Pl0p/Gate_O_Matix/Kicad_Project/My_library/Mes_modèles_3D/bh-connector-set-1.snapshot.1/BH-16R.STEP

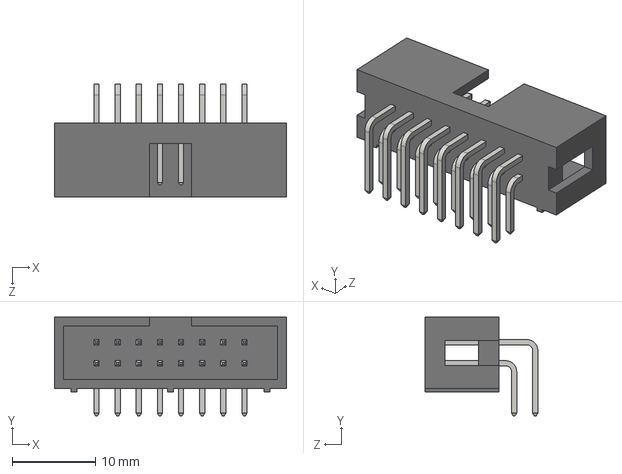
[picture p14: CAD file, 2021-02-21]
Kicad_Project/My_library/Mes_modèles_3D/bh-connector-set-1.snapshot.1/BH-16R.STEP
27.9 x 11.9 x 13.6 mm
