Pl0p/Gate_O_Matix/Kicad_Project/My_library/Mes_modèles_3D/Encoders/EC11B-SW-Vert-20F-green.step

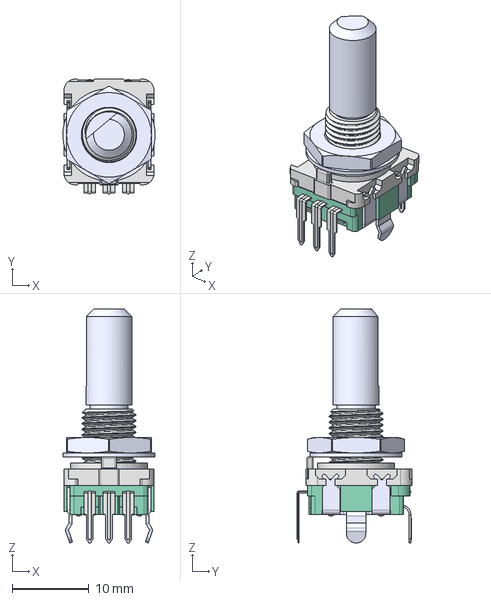
[picture p15: CAD file, 2021-02-21]
Kicad_Project/My_library/Mes_modèles_3D/Encoders/EC11B-SW-Vert-20F-green.step
12.0 x 14.9 x 30.4 mm
