Pl0p/Gate_O_Matix/Kicad_Project/My_library/Mes_modèles_3D/Encoders/EC11B-SW-Vert-15K-blue.step

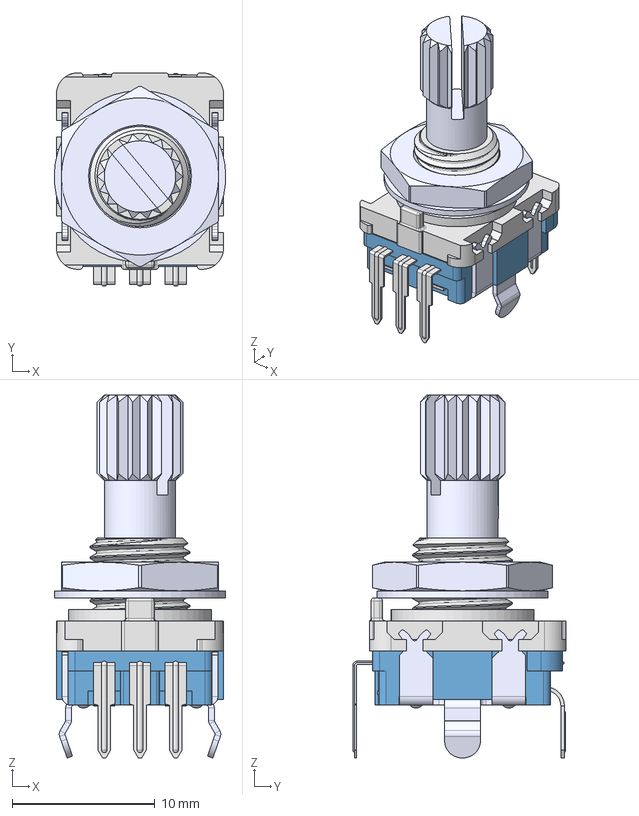
[picture p20: CAD file, 2021-02-21]
Kicad_Project/My_library/Mes_modèles_3D/Encoders/EC11B-SW-Vert-15K-blue.step
12.0 x 14.9 x 25.4 mm
