Pl0p/Gate_O_Matix/Kicad_Project/My_library/Mes_modèles_3D/IC_Sockets/DIP-32 W7.62mm IC with Socket.stp

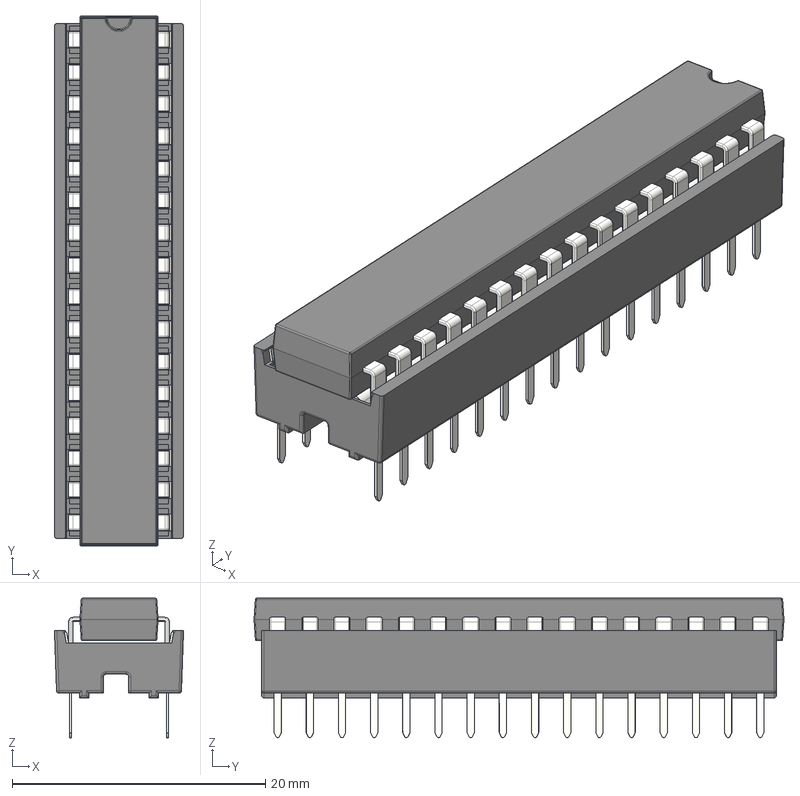
[picture p21: CAD file, 2021-02-21]
Kicad_Project/My_library/Mes_modèles_3D/IC_Sockets/DIP-32 W7.62mm IC with Socket.stp
10.2 x 41.8 x 11.0 mm
Stamped Dual Wipe Contact for DIP Sockets x 32
Body DIP-48 Socket
IC Beinchen x 32
DIP-32 W7.62
