Pl0p/Gate_O_Matix/Kicad_Project/My_library/Mes_modèles_3D/IC_Sockets/DIP-18 W7.62mm IC with Socket.stp

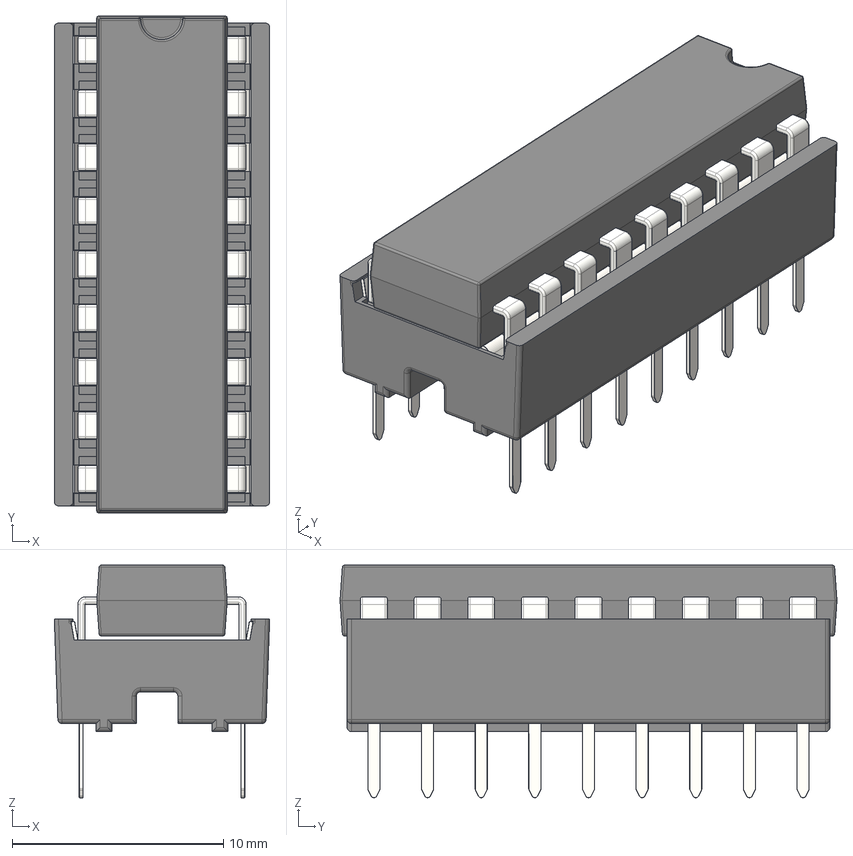
[picture p22: CAD file, 2021-02-21]
Kicad_Project/My_library/Mes_modèles_3D/IC_Sockets/DIP-18 W7.62mm IC with Socket.stp
10.2 x 23.5 x 11.0 mm
Stamped Dual Wipe Contact for DIP Sockets x 18
Body DIP-18 P7.62mm Socket
IC Beinchen x 18
DIP-18 W7.62
