Pl0p/Gate_O_Matix/Kicad_Project/My_library/Mes_modèles_3D/Encoders/EC11B-SW-Vert-20K-green.step

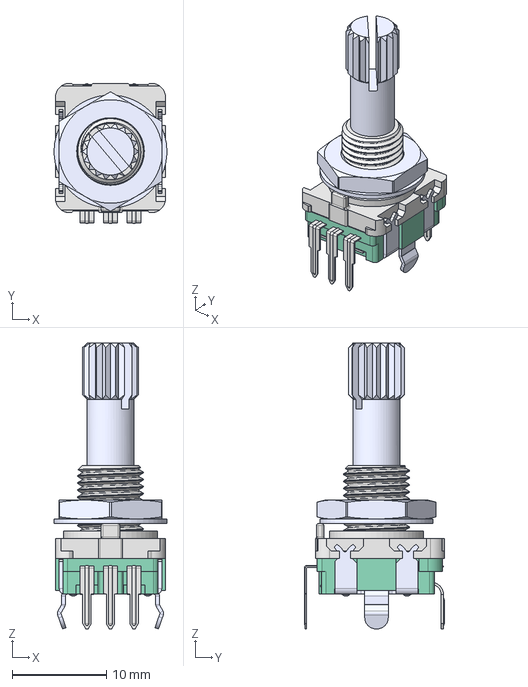
[picture p23: CAD file, 2021-02-21]
Kicad_Project/My_library/Mes_modèles_3D/Encoders/EC11B-SW-Vert-20K-green.step
12.0 x 14.9 x 30.4 mm
